4x1md/nikon_gps/mechanics/6x6 button.png

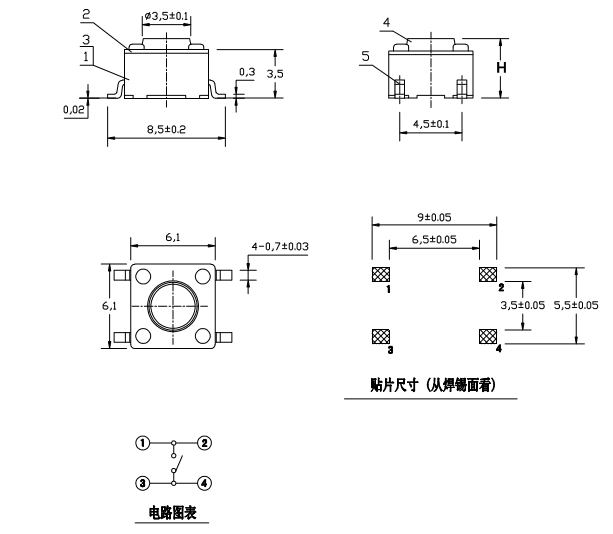
mechanics/6x6 button.png
