4x1md/nikon_gps/mechanics/CASE-020 SIZE.jpg

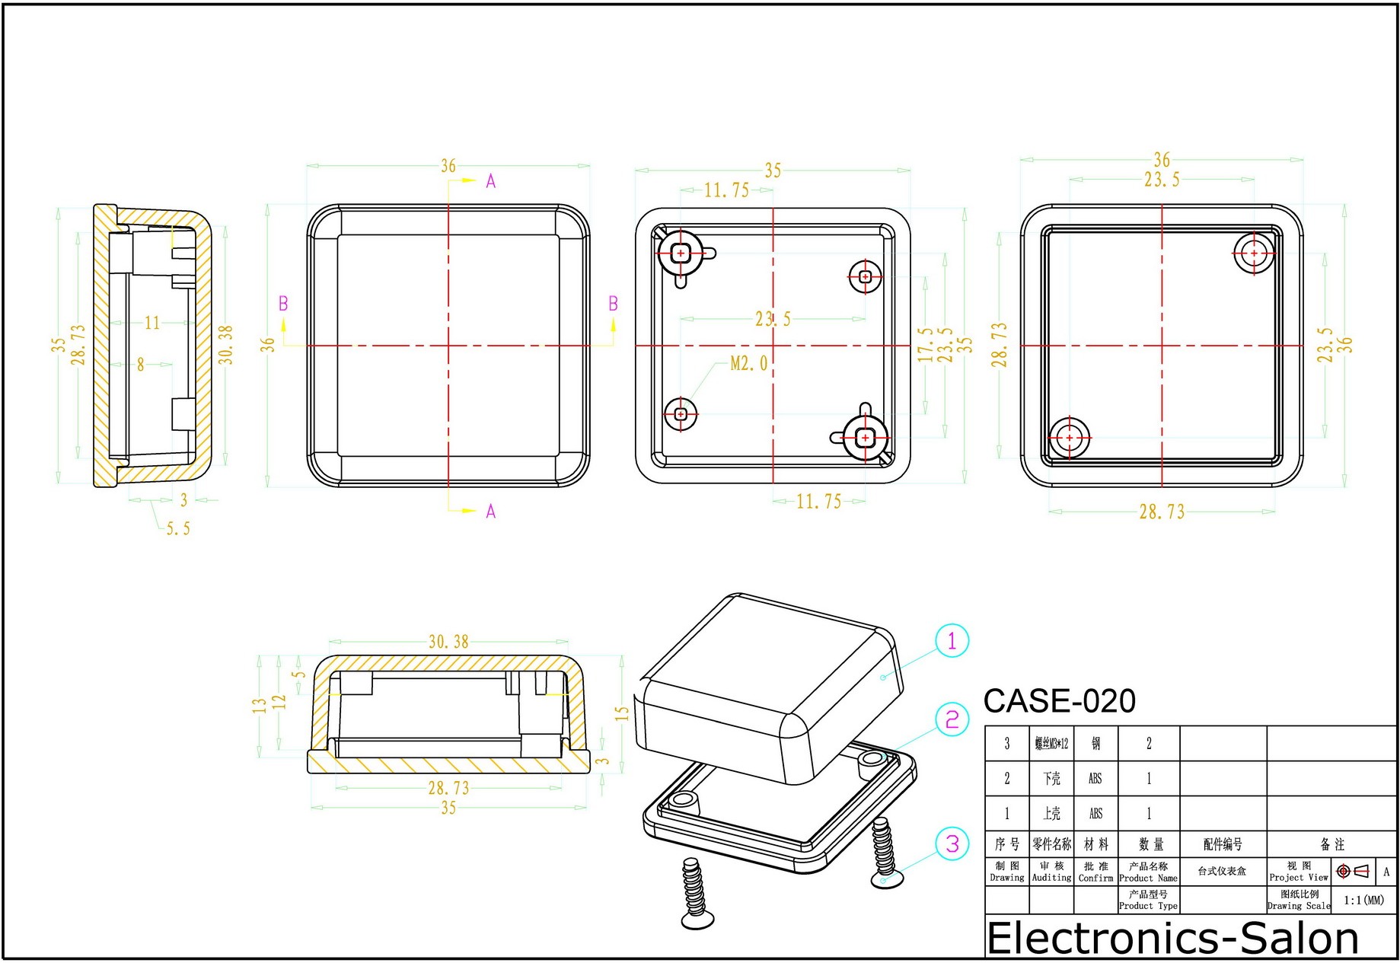
mechanics/CASE-020 SIZE.jpg
