4x1md/nikon_gps/mechanics/pcb_with_dimensions.png

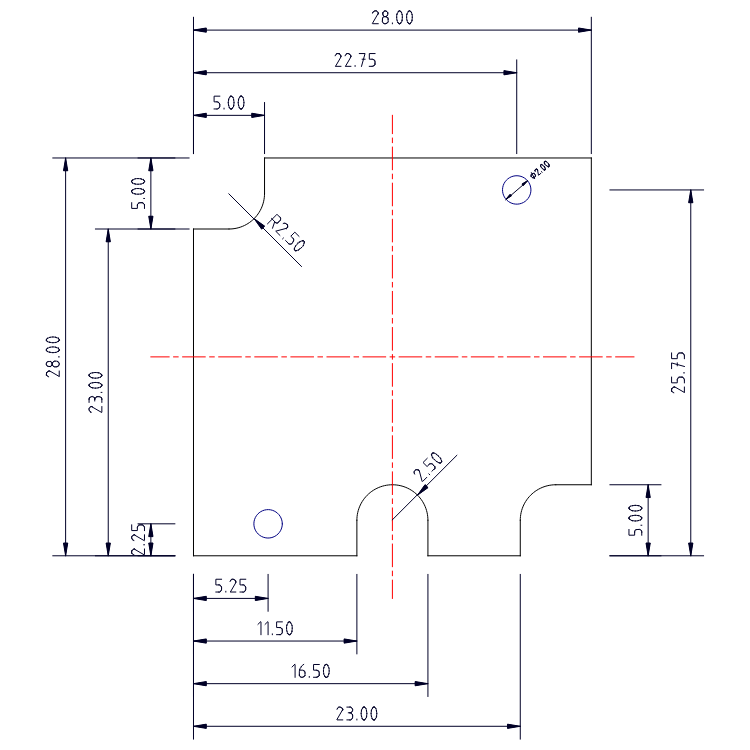
mechanics/pcb_with_dimensions.png
