4x1md/nikon_gps/images/rev-b-tests/SCREEN_1.png

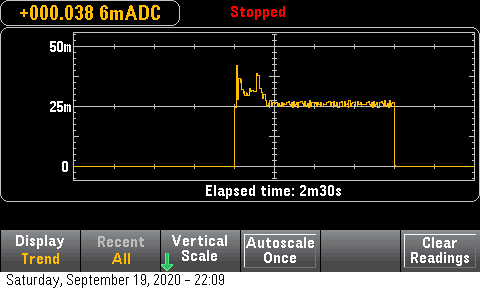
images/rev-b-tests/SCREEN_1.png
