4x1md/nikon_gps/images/rev-b-tests/SCREEN_3.png

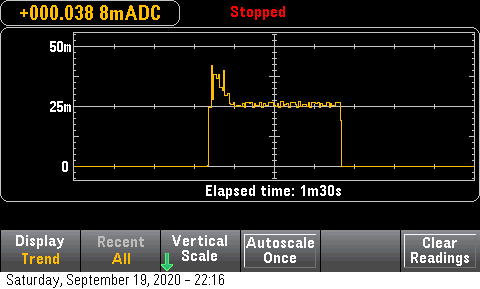
images/rev-b-tests/SCREEN_3.png
