4x1md/nikon_gps/simulations/gps-3.3v-decoupling.asc

C1: cap; 1µ; Rser=0.02
L1: ind; 1µ; Rser=0.68
R1: res; 680
V1: voltage; PULSE(3.2825 3.3175 10u 4u 50u 0 54u)
Named nets: 0, in, out
.tran 0 1m 0 0.01u
