4x1md/nikon_gps/simulations/adp2108.asc

C1: cap; 10µ
C2: cap; 4.7µ
C3: cap; 1100n
L1: ind; 1.0µ
L2: FerriteBead; 2.5µ; Ipk=1 Rser=0.157 Rpar=605 Cpar=1.1p
R1: EuropeanResistor; 66K
R2: res; 0.01
U1: ADP2108-3.3
V1: voltage; 5.5V
Named nets: 0, OUT, sw, OUT_FILT
.tran 50m
