4x1md/nikon_gps/simulations/debouncing_schmitt.asc

A1: schmtinv; Vhigh=3.3 Vt=1.22 Vh=0.28 Trise=50n Tfall=50n
C1: cap; 100n
R1: res; 33K
R2: res; 4.7K
S1: sw; PushBtn
V1: voltage; PULSE(0 3.3 1m 150u 10m 1s)
V2: voltage; PULSE(0 1.0 30m 1n 1n 30m 100m 1)
V3: voltage; PULSE(0 -1.0 30m 1n 1n 0.25m 0.5m 10)
V4: voltage; PULSE(0 1.0 60m 0 0 0.25m 0.5m 10)
Named nets: 0, OUT, IN, cap, Vcc, sw_ctrl
.model PushBtn SW(Roff=100Meg Ron=1.0 Vt=0.5 Vh=0)
.tran 0 100m 0 500n
TI SN74LVC1G14
100msec pulse
Turn-on bouncing
Turn-off bouncing
