4x1md/nikon_gps/simulations/level_shifter_1.8-5.0.asc

C1: cap; 10p
Q1: npn; 2N2222
Q2: nmos; 2N7002
R1: EuropeanResistor; 10K; tol=1 pwr=0.1
R2: EuropeanResistor; 10K; tol=1 pwr=0.1
R3: EuropeanResistor; 4.7K; tol=1 pwr=0.1
V1: voltage; PULSE(0.4 1.35 0 100n 100n 50u 100u)
V2: voltage; 3.3V
V3: voltage; 5.5V
Named nets: 0, OUT, IN
.tran 0 0.25m 0 10n
